ryansalehi/eecs_vending_machine/Project_Images/happy.png

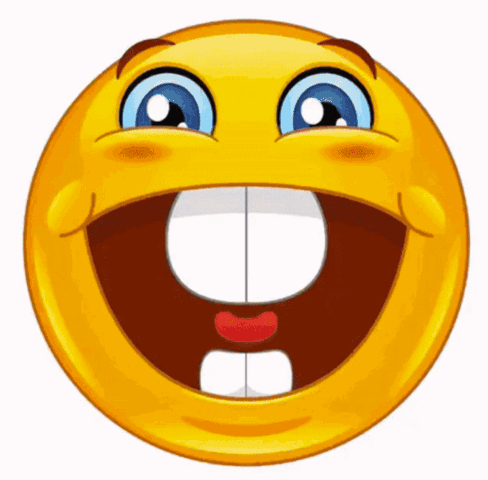
Project_Images/happy.png
