ryansalehi/eecs_vending_machine/MCU_A_v2_0/Core/Inc/happy_out.h

#pragma once
#include <stdint.h>

// RGB888 byte order: R, G, B for each pixel
static const uint8_t happy_out[100*100*3] = {
    0xFE, 0xFA, 0xFC, 0xFE, 0xFA, 0xFC, 0xFE, 0xFA, 0xFC, 0xFE, 0xFA, 0xFC, 
    0xFE, 0xFA, 0xFC, 0xFE, 0xFA, 0xFC, 0xFE, 0xFA, 0xFC, 0xFE, 0xFA, 0xFC, 
    0xFE, 0xFA, 0xFC, 0xFE, 0xFA, 0xFC, 0xFE, 0xFA, 0xFC, 0xFE, 0xFA, 0xFC, 
    0xFE, 0xFA, 0xFC, 0xFE, 0xFA, 0xFC, 0xFE, 0xFA, 0xFC, 0xFE, 0xFA, 0xFC, 
    0xFE, 0xFA, 0xFC, 0xFE, 0xFA, 0xFC, 0xFE, 0xFA, 0xFC, 0xFE, 0xFA, 0xFC, 
    0xFE, 0xFA, 0xFC, 0xFE, 0xFA, 0xFC, 0xFE, 0xFA, 0xFC, 0xFE, 0xFA, 0xFC, 
    0xFE, 0xFA, 0xFC, 0xFE, 0xFA, 0xFC, 0xFE, 0xFA, 0xFC, 0xFE, 0xFA, 0xFC, 
    0xFE, 0xFA, 0xFC, 0xFE, 0xFA, 0xFC, 0xFE, 0xFA, 0xFC, 0xFE, 0xFA, 0xFC, 
    0xFE, 0xFA, 0xFC, 0xFE, 0xFA, 0xFC, 0xFE, 0xFA, 0xFC, 0xFE, 0xFA, 0xFC, 
    0xFE, 0xFA, 0xFC, 0xFE, 0xFA, 0xFC, 0xFE, 0xFA, 0xFC, 0xFE, 0xFA, 0xFC, 
    0xFE, 0xFA, 0xFC, 0xFE, 0xFA, 0xFC, 0xFE, 0xFA, 0xFC, 0xFE, 0xFA, 0xFC, 
    0xFE, 0xFA, 0xFC, 0xFE, 0xFA, 0xFC, 0xFE, 0xFA, 0xFC, 0xFE, 0xFA, 0xFC, 
    0xFE, 0xFA, 0xFC, 0xFE, 0xFA, 0xFC, 0xFE, 0xFA, 0xFC, 0xFE, 0xFA, 0xFC, 
    0xFE, 0xFA, 0xFC, 0xFE, 0xFA, 0xFC, 0xFE, 0xFA, 0xFC, 0xFE, 0xFA, 0xFC, 
    0xFE, 0xFA, 0xFC, 0xFE, 0xFA, 0xFC, 0xFE, 0xFA, 0xFC, 0xFE, 0xFA, 0xFC, 
    0xFE, 0xFA, 0xFC, 0xFE, 0xFA, 0xFC, 0xFE, 0xFA, 0xFC, 0xFE, 0xFA, 0xFC, 
    0xFE, 0xFA, 0xFC, 0xFE, 0xFA, 0xFC, 0xFE, 0xFA, 0xFC, 0xFE, 0xFA, 0xFC, 
    0xFE, 0xFA, 0xFC, 0xFE, 0xFA, 0xFC, 0xFE, 0xFA, 0xFC, 0xFE, 0xFA, 0xFC, 
    0xFE, 0xFA, 0xFC, 0xFE, 0xFA, 0xFC, 0xFE, 0xFA, 0xFC, 0xFE, 0xFA, 0xFC, 
    0xFE, 0xFA, 0xFC, 0xFE, 0xFA, 0xFC, 0xFE, 0xFA, 0xFC, 0xFE, 0xFA, 0xFC, 
    0xFE, 0xFA, 0xFC, 0xFE, 0xFA, 0xFC, 0xFE, 0xFA, 0xFC, 0xFE, 0xFA, 0xFC, 
    0xFE, 0xFA, 0xFC, 0xFE, 0xFA, 0xFC, 0xFE, 0xFA, 0xFC, 0xFE, 0xFA, 0xFC, 
    0xFE, 0xFA, 0xFC, 0xFE, 0xFA, 0xFC, 0xFE, 0xFA, 0xFC, 0xFE, 0xFA, 0xFC, 
    0xFE, 0xFA, 0xFC, 0xFE, 0xFA, 0xFC, 0xFE, 0xFA, 0xFC, 0xFE, 0xFA, 0xFC, 
    0xFE, 0xFA, 0xFC, 0xFE, 0xFA, 0xFC, 0xFE, 0xFA, 0xFC, 0xFE, 0xFA, 0xFC, 
    0xFE, 0xFA, 0xFC, 0xFE, 0xFA, 0xFC, 0xFE, 0xFA, 0xFC, 0xFE, 0xFA, 0xFC, 
    0xFE, 0xFA, 0xFC, 0xFE, 0xFA, 0xFC, 0xFE, 0xFA, 0xFC, 0xFE, 0xFA, 0xFC, 
    0xFE, 0xFA, 0xFC, 0xFE, 0xFA, 0xFC, 0xFE, 0xFA, 0xFC, 0xFE, 0xFA, 0xFC, 
    0xFE, 0xFA, 0xFC, 0xFE, 0xFA, 0xFC, 0xFE, 0xFA, 0xFC, 0xFE, 0xFA, 0xFC, 
    0xFE, 0xFA, 0xFC, 0xFE, 0xFA, 0xFC, 0xFE, 0xFA, 0xFC, 0xFE, 0xFA, 0xFC, 
    0xFE, 0xFA, 0xFC, 0xFE, 0xFA, 0xFC, 0xFE, 0xFA, 0xFC, 0xFE, 0xFA, 0xFC, 
    0xFE, 0xFA, 0xFC, 0xFE, 0xFA, 0xFC, 0xFE, 0xFA, 0xFC, 0xFE, 0xFA, 0xFC, 
    0xFE, 0xFA, 0xFC, 0xFE, 0xFA, 0xFC, 0xFE, 0xFA, 0xFC, 0xFE, 0xFA, 0xFC, 
    0xFE, 0xFA, 0xFC, 0xFE, 0xFA, 0xFC, 0xFE, 0xFA, 0xFC, 0xFE, 0xFA, 0xFC, 
    0xFE, 0xFA, 0xFC, 0xFE, 0xFA, 0xFC, 0xFE, 0xFA, 0xFC, 0xFE, 0xFA, 0xFC, 
    0xFE, 0xFA, 0xFC, 0xFE, 0xFA, 0xFC, 0xFE, 0xFA, 0xFC, 0xFE, 0xFA, 0xFC, 
    0xFE, 0xFA, 0xFC, 0xFE, 0xFA, 0xFC, 0xFE, 0xFA, 0xFC, 0xFE, 0xFA, 0xFB, 
    0xFE, 0xF9, 0xFB, 0xFD, 0xF9, 0xFB, 0xFD, 0xF9, 0xFB, 0xFD, 0xF9, 0xFB, 
    0xFE, 0xF9, 0xFB, 0xFE, 0xFA, 0xFB, 0xFE, 0xFA, 0xFC, 0xFE, 0xFA, 0xFC, 
    0xFE, 0xFA, 0xFC, 0xFE, 0xFA, 0xFC, 0xFE, 0xFA, 0xFC, 0xFE, 0xFA, 0xFC, 
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
};
