ryansalehi/eecs_vending_machine/MCU_B_v2_0/Core/Src/latch.c

#include "latch.h"
#include "main.h"

void LATCH_Open(LATCHES latch)
{
    if(latch == door)
    {
        HAL_GPIO_WritePin(GPIOC, GPIO_PIN_2, GPIO_PIN_SET);
        HAL_Delay(2500);
        HAL_GPIO_WritePin(GPIOC, GPIO_PIN_2, GPIO_PIN_RESET);
        return;
    }
    if (latch == tokendrop)
    {
        HAL_GPIO_WritePin(GPIOC, GPIO_PIN_3, GPIO_PIN_SET);
        HAL_Delay(1000);
        HAL_GPIO_WritePin(GPIOC, GPIO_PIN_3, GPIO_PIN_RESET);
        return;
    }
}
